asdfgadsfff/Cantleaver-Monitor-Arm-Mount-for-Dorm-Desk/First Design/l bracket after modification.SLDPRT

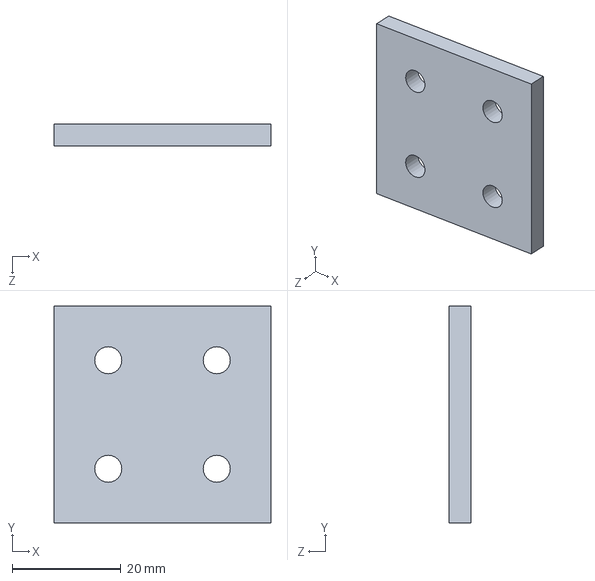
[picture p8: CAD file, 2021-08-26]
First Design/l bracket after modification.SLDPRT
40.0 x 40.0 x 4.00 mm
